cm68/WiFiDongle/FreeSans8pt7b.h

const uint8_t FreeSans8pt7bBitmaps[] PROGMEM = {
  0x00, 0xFF, 0xB0, 0xBB, 0xA8, 0x13, 0x09, 0x04, 0x8F, 0xF3, 0x21, 0x90,
  0x99, 0xFE, 0x24, 0x12, 0x19, 0x00, 0x10, 0xFA, 0x5C, 0x99, 0x1E, 0x0F,
  0x0B, 0x13, 0x26, 0x5B, 0xE1, 0x02, 0x00, 0x38, 0x41, 0x31, 0x0C, 0x48,
  0x11, 0x20, 0x79, 0x00, 0x04, 0x00, 0x27, 0x81, 0xB3, 0x04, 0x84, 0x23,
  0x30, 0x87, 0x80, 0x3C, 0x32, 0x11, 0x05, 0x83, 0x83, 0xC3, 0x35, 0x0E,
  0x86, 0x63, 0x9F, 0x60, 0xF0, 0x12, 0x64, 0x4C, 0xC8, 0x8C, 0xC4, 0x42,
  0x20, 0x91, 0x26, 0x49, 0x24, 0xA4, 0xA0, 0x22, 0xF6, 0x90, 0x10, 0x10,
  0x10, 0x10, 0xFF, 0x10, 0x10, 0x10, 0xF5, 0xF0, 0xF0, 0x00, 0x84, 0x22,
  0x10, 0x88, 0x42, 0x21, 0x00, 0x7D, 0x8B, 0x1C, 0x18, 0x30, 0x60, 0xC1,
  0x87, 0x89, 0xF0, 0x37, 0xF3, 0x33, 0x33, 0x33, 0x30, 0x7D, 0x8E, 0x0C,
  0x10, 0x61, 0x8E, 0x30, 0xC1, 0x03, 0xF8, 0x7D, 0x8E, 0x18, 0x30, 0xC3,
  0x81, 0x81, 0x83, 0x8D, 0xF0, 0x06, 0x0E, 0x0E, 0x16, 0x26, 0x66, 0x46,
  0xFF, 0x06, 0x06, 0x06, 0x7E, 0x83, 0x06, 0x0F, 0xD8, 0xC0, 0x81, 0x83,
  0x8D, 0xF0, 0x7C, 0x8F, 0x0C, 0x0B, 0xD8, 0xE0, 0xC1, 0x83, 0x8D, 0xF0,
  0xFE, 0x04, 0x10, 0x60, 0x82, 0x04, 0x18, 0x20, 0x41, 0x80, 0x7D, 0x8E,
  0x1E, 0x37, 0xCF, 0xA1, 0xC1, 0x83, 0x8D, 0xF0, 0x7D, 0x8A, 0x1C, 0x18,
  0x78, 0xDE, 0x81, 0x87, 0x89, 0xE0, 0xC0, 0x0F, 0xF0, 0x03, 0xD4, 0x01,
  0x07, 0x1C, 0xE0, 0xC0, 0x70, 0x0E, 0x03, 0xFF, 0x00, 0x00, 0xFF, 0x00,
  0xC0, 0x38, 0x0E, 0x03, 0x1C, 0x70, 0x80, 0x38, 0xDF, 0x0E, 0x10, 0x61,
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
  {   332,   8,  12,  10,    1,  -11 },   // 0x46 'F'
  {   344,  10,  12,  12,    1,  -11 },   // 0x47 'G'
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

const GFXfont FreeSans8pt7b PROGMEM = {
  (uint8_t  *)FreeSans8pt7bBitmaps,
  (GFXglyph *)FreeSans8pt7bGlyphs,
  0x20, 0x7E, 17 };

// Approx. 1574 bytes
